DimaDaria/Tone-Control-Preamplifier/Layout/ALL LAYERS 2.PNG

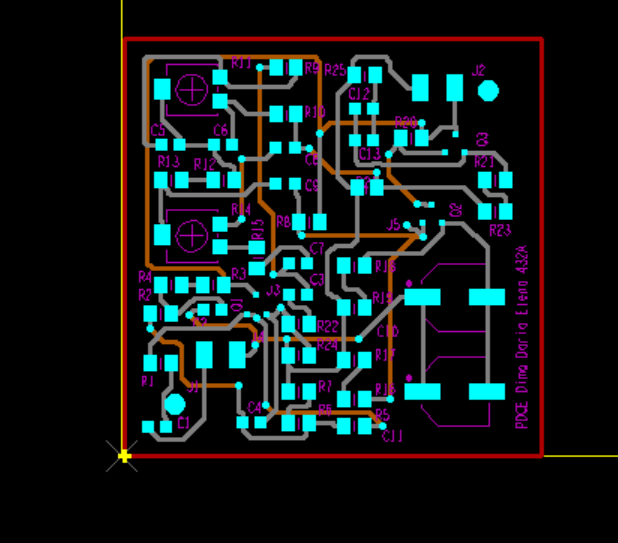
Layout/ALL LAYERS 2.PNG
