DimaDaria/Tone-Control-Preamplifier/Layout/ALL LAYERS 3.PNG

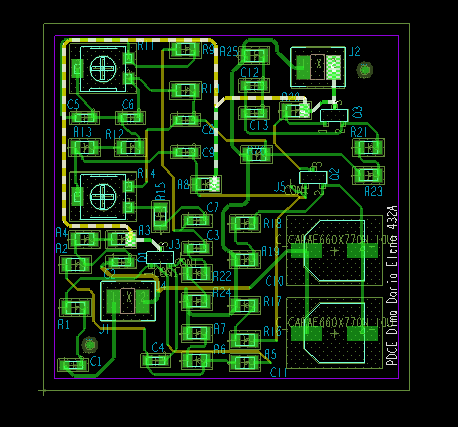
Layout/ALL LAYERS 3.PNG
