DimaDaria/Tone-Control-Preamplifier/Simulations/pozitie_mediana_freq.PNG

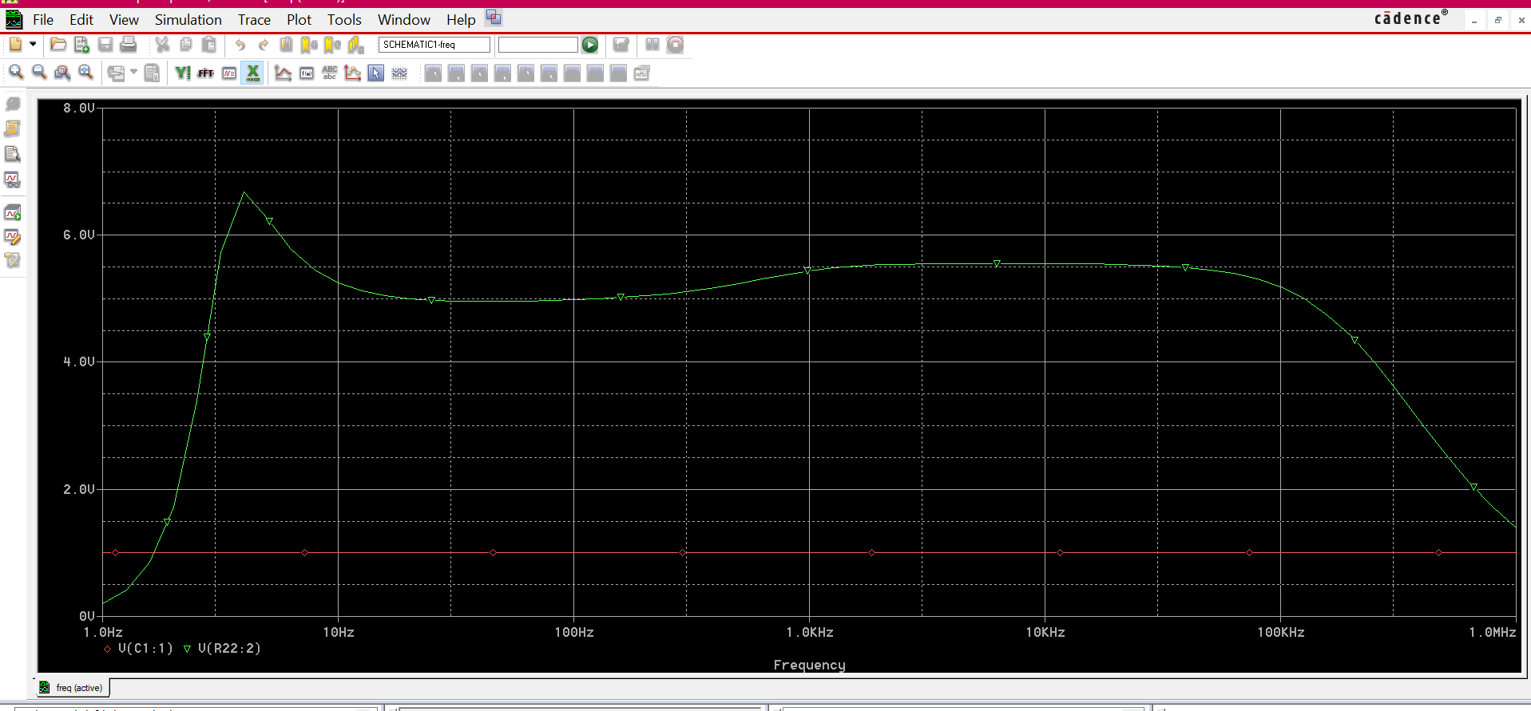
Simulations/pozitie_mediana_freq.PNG
