DimaDaria/Tone-Control-Preamplifier/Simulations/simulare_frecventa_pozitie_accentuata_inalte_2.PNG

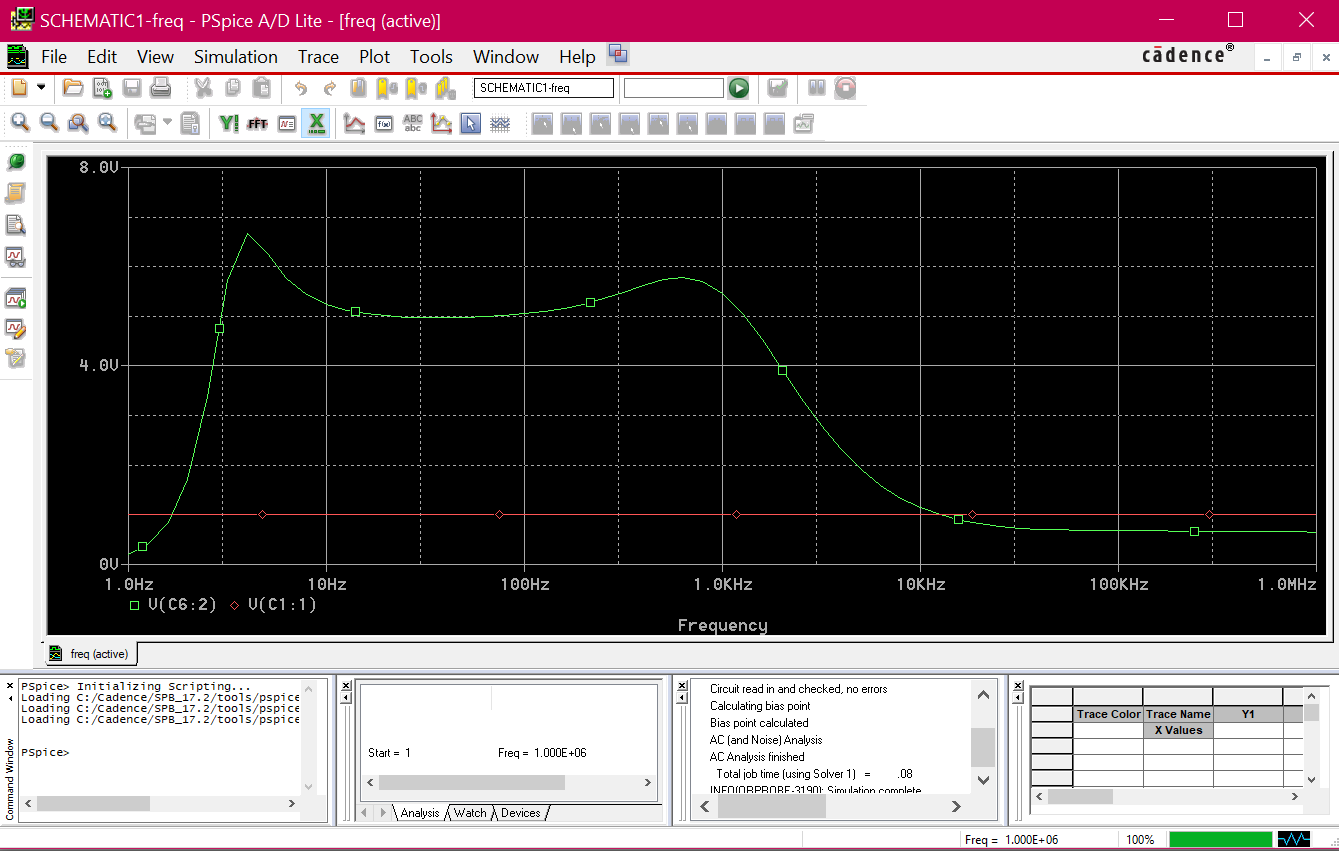
Simulations/simulare_frecventa_pozitie_accentuata_inalte_2.PNG
