DimaDaria/Tone-Control-Preamplifier/Simulations/simulare_frecventa_pozitie_accentuate_inalte_1.PNG

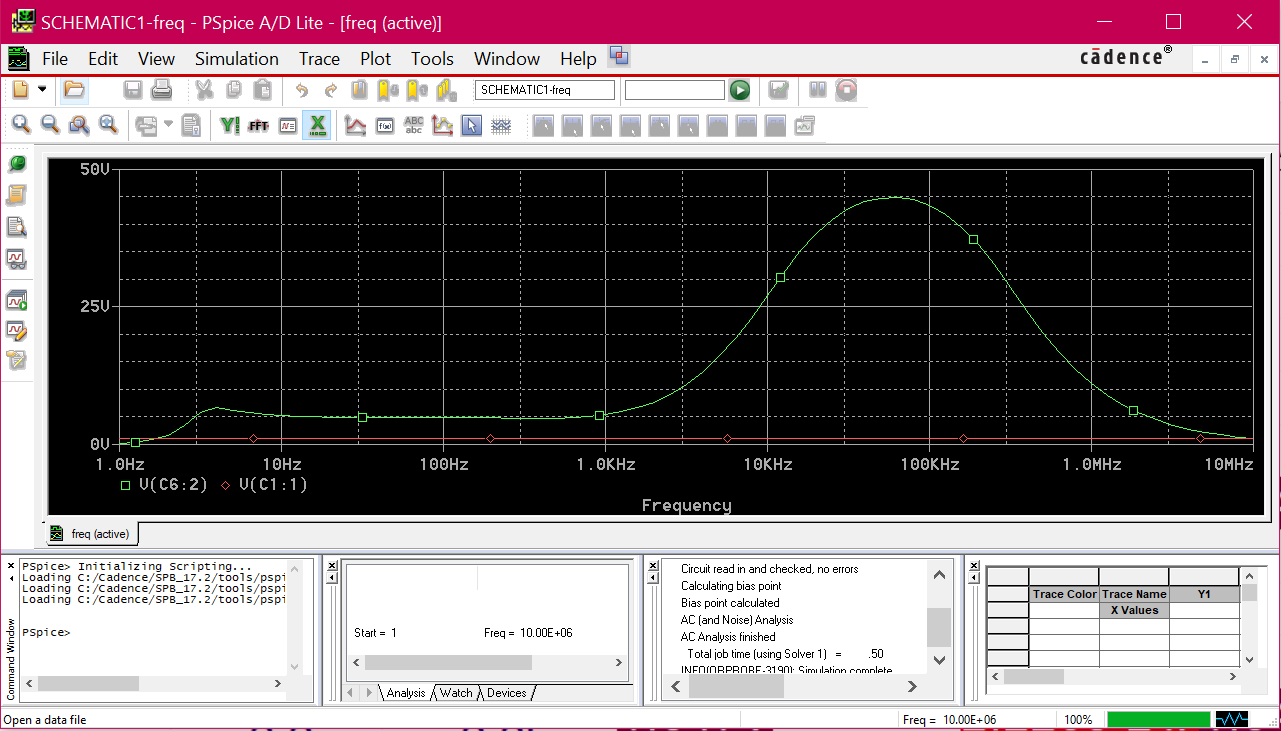
Simulations/simulare_frecventa_pozitie_accentuate_inalte_1.PNG
