DimaDaria/Tone-Control-Preamplifier/Simulations/simulare_frecventa_pozitie_accentuate_joase_2.PNG

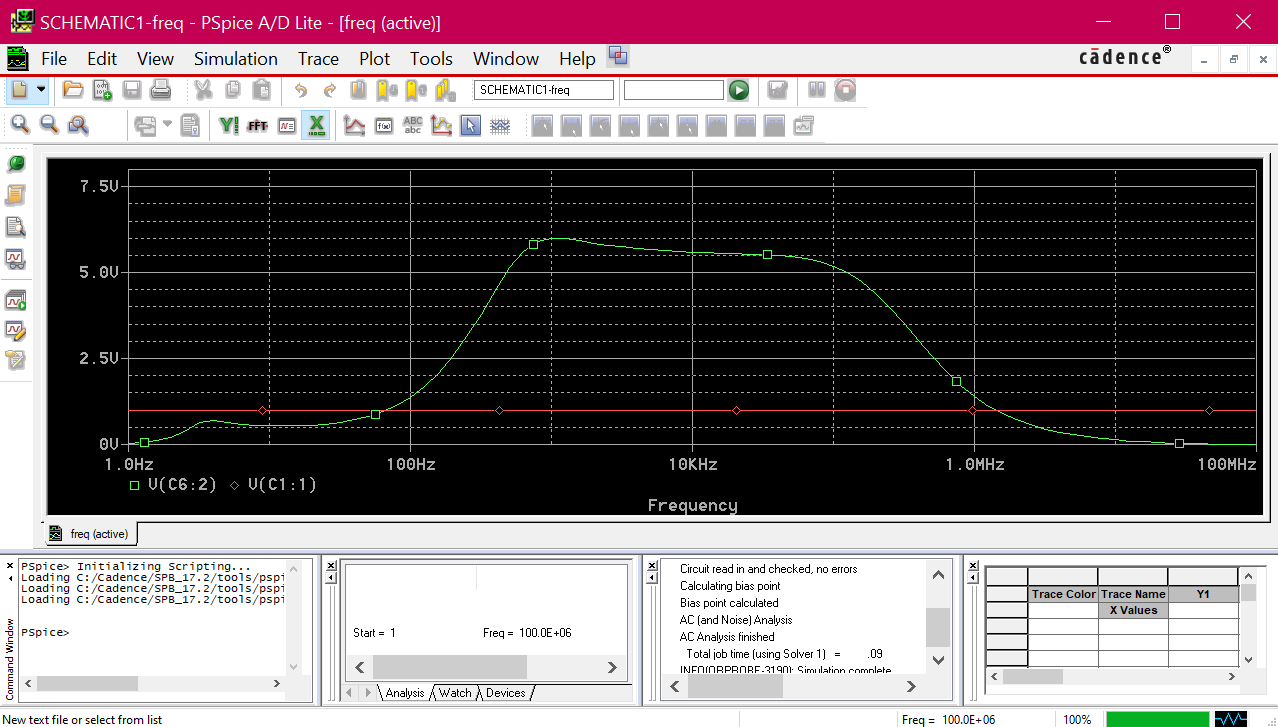
Simulations/simulare_frecventa_pozitie_accentuate_joase_2.PNG
